BrianEnigma/InfoNinja/design_documents/parts_list.png

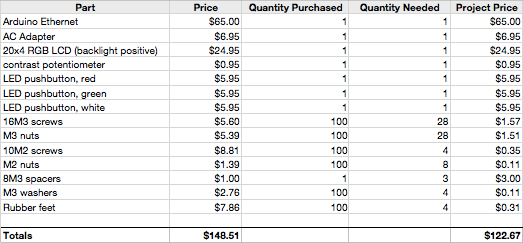
design_documents/parts_list.png
